tom-f-oconnell/firepick-delta/docs/STL images/3D0015a - EMC02 mounting plate.png

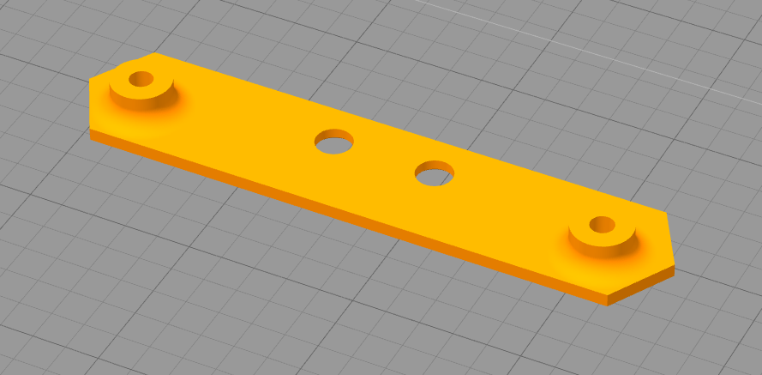
docs/STL images/3D0015a - EMC02 mounting plate.png
