tom-f-oconnell/firepick-delta/docs/STL images/3D0021 - EMC01 Modular tool card-cage.png

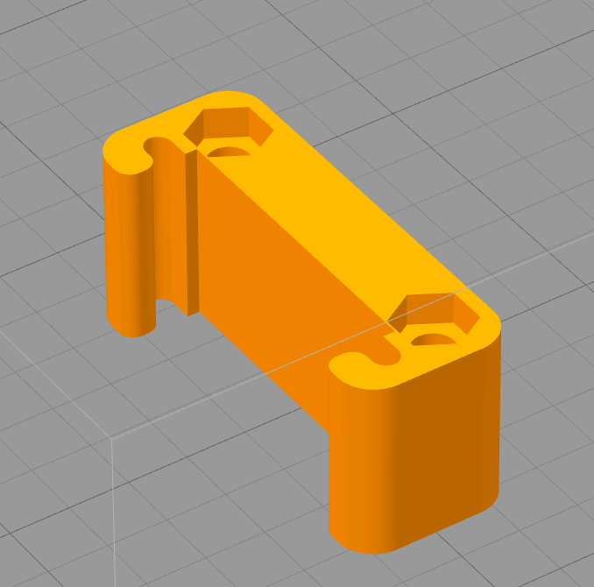
docs/STL images/3D0021 - EMC01 Modular tool card-cage.png
