tom-f-oconnell/firepick-delta/docs/STL images/3D0052a - Heated Bed Bracket.png

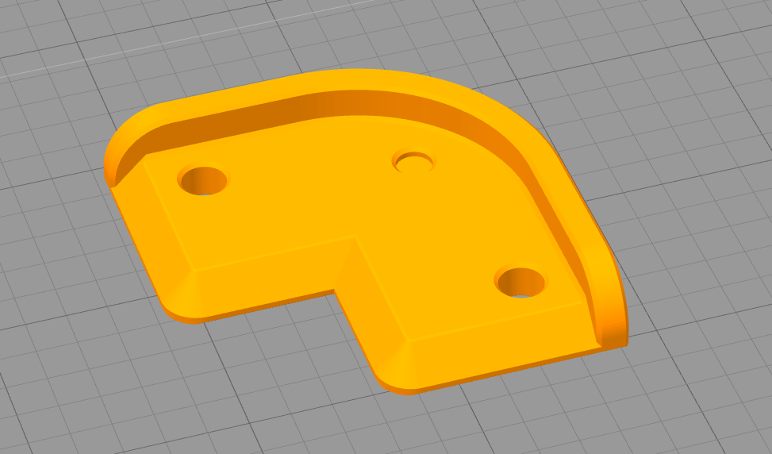
docs/STL images/3D0052a - Heated Bed Bracket.png
