tom-f-oconnell/firepick-delta/docs/STL images/3D0456c Delta stepper mount.png

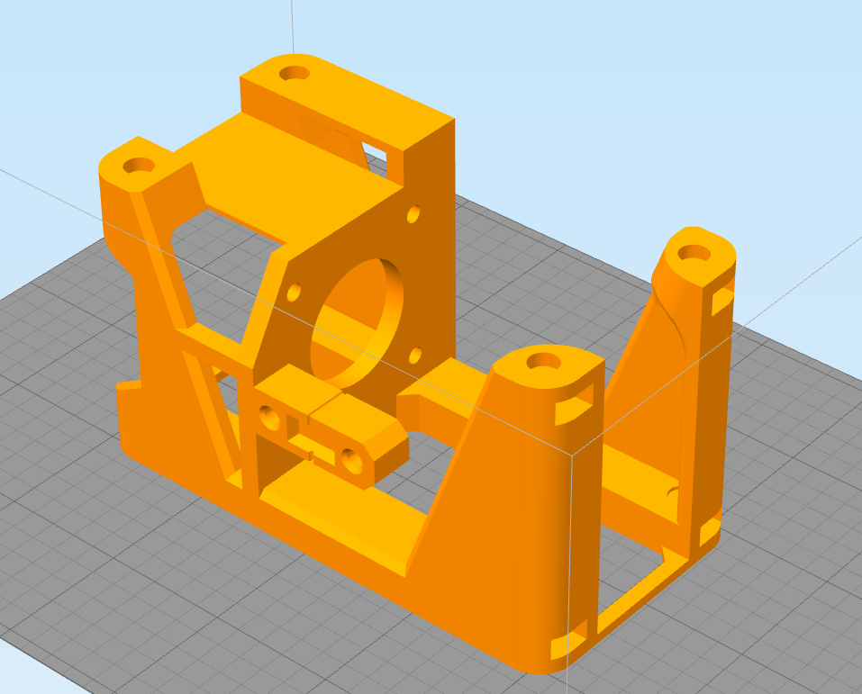
docs/STL images/3D0456c Delta stepper mount.png
