tom-f-oconnell/firepick-delta/docs/STL images/3DAT0001a - Wade extruder body.png

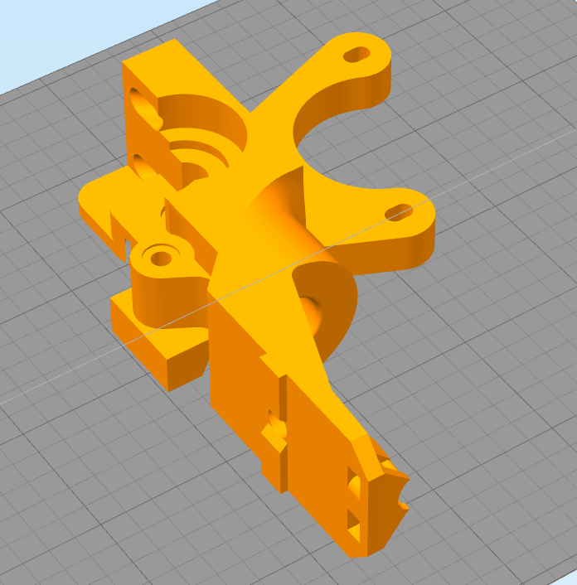
docs/STL images/3DAT0001a - Wade extruder body.png
