tom-f-oconnell/firepick-delta/docs/STL images/3DAT0002 - Wade large gear (herringbone).png

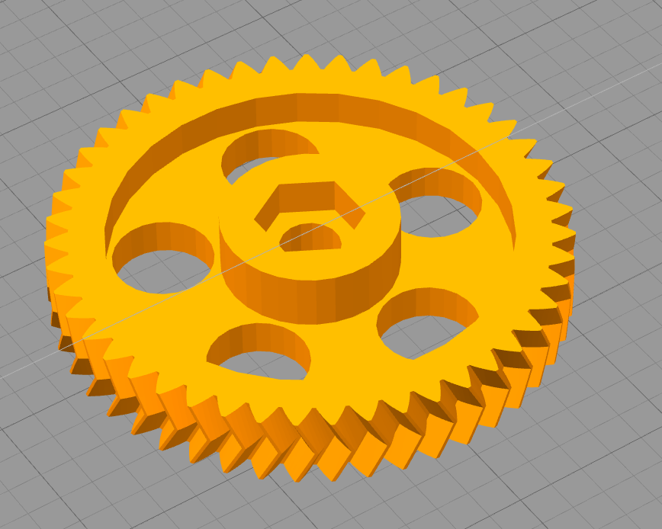
docs/STL images/3DAT0002 - Wade large gear (herringbone).png
