tom-f-oconnell/firepick-delta/docs/STL images/3DAT0003 - Wade small gear (herringbone).png

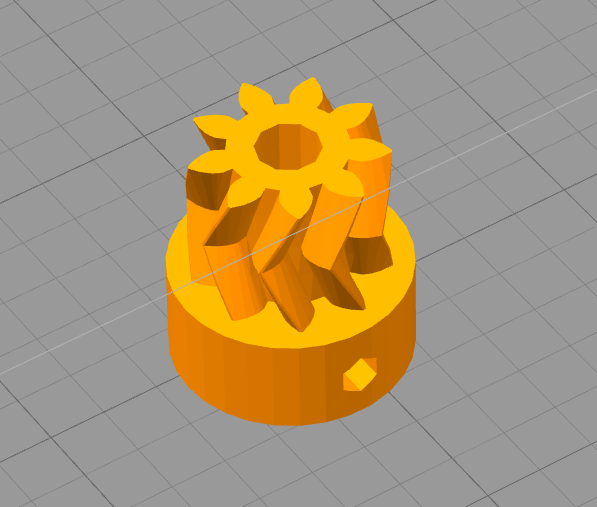
docs/STL images/3DAT0003 - Wade small gear (herringbone).png
