tom-f-oconnell/firepick-delta/docs/STL images/3DAT004 - Guidler.png

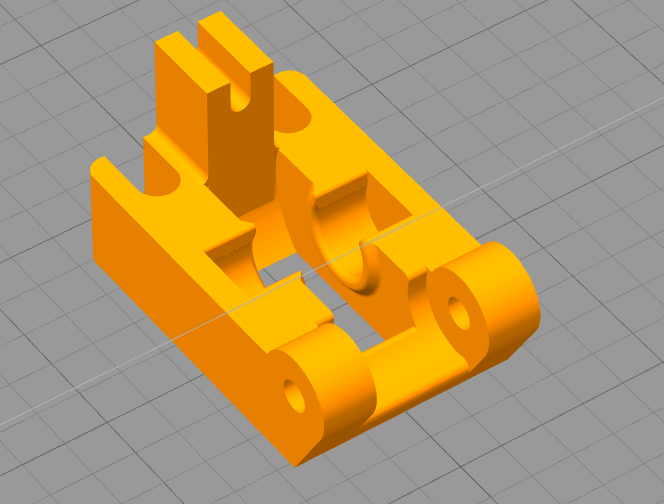
docs/STL images/3DAT004 - Guidler.png
