tom-f-oconnell/firepick-delta/docs/STL images/3DAT0011a - End effector - ATC hub (top).png

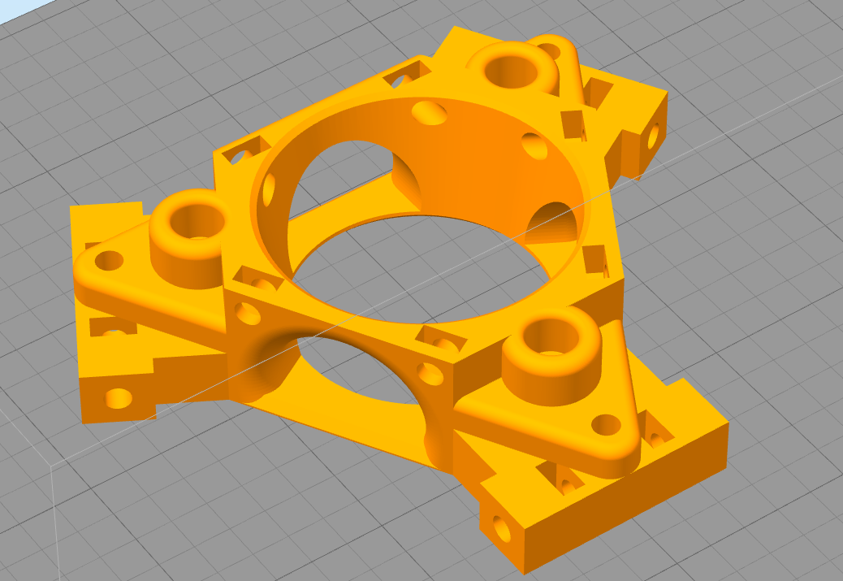
docs/STL images/3DAT0011a - End effector - ATC hub (top).png
