tom-f-oconnell/firepick-delta/docs/STL images/3DAT0015c - Camera-to-end-effector mount - downward endocam.png

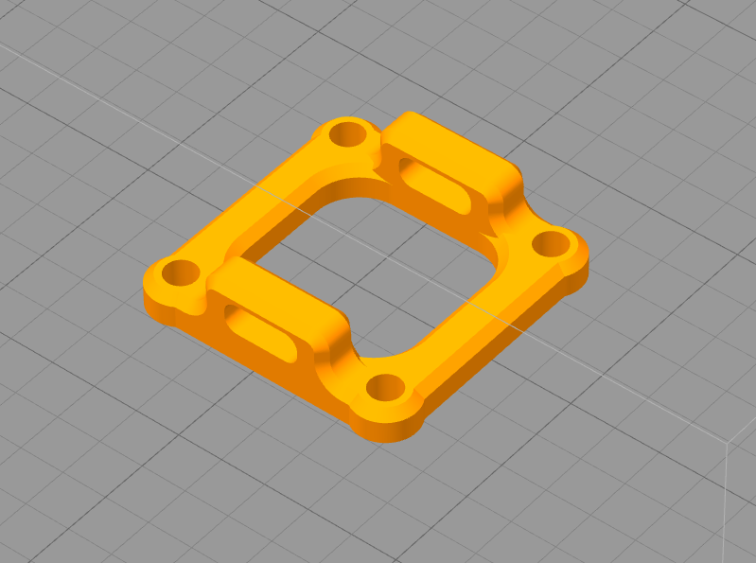
docs/STL images/3DAT0015c - Camera-to-end-effector mount - downward endocam.png
