tom-f-oconnell/firepick-delta/docs/STL images/3DAT0021a - NEMA8 mount.png

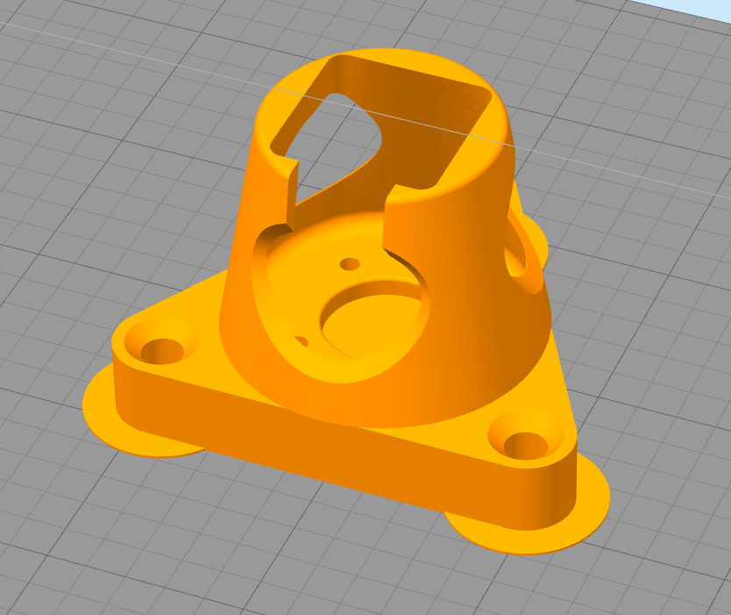
docs/STL images/3DAT0021a - NEMA8 mount.png
