tom-f-oconnell/firepick-delta/docs/STL images/FSTN-M3-14L-UNTHREADED.png

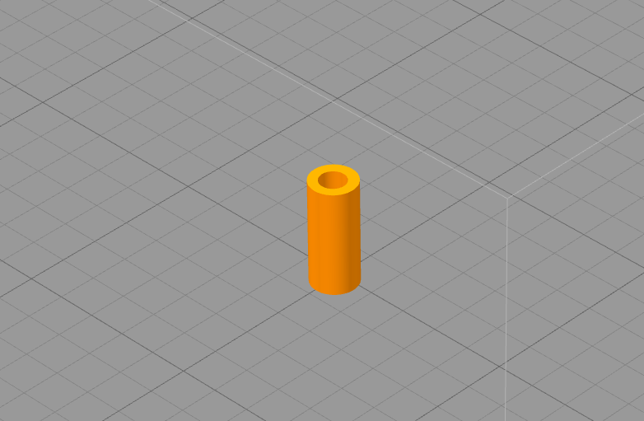
docs/STL images/FSTN-M3-14L-UNTHREADED.png
