tom-f-oconnell/firepick-delta/production/3D printed pieces - STL - Orange/3DAT0015c - Camera-to-end-effector mount - downward endocam.stl

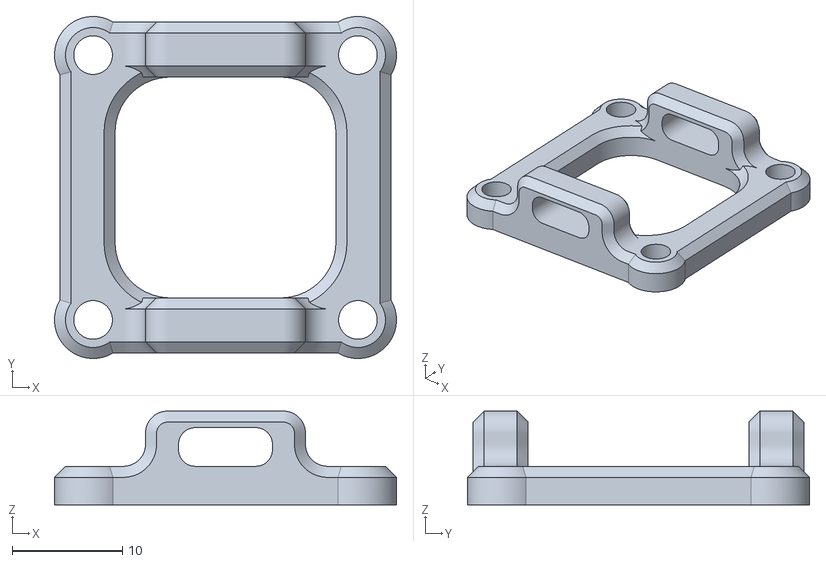
[picture p34: CAD file, 2017-01-31]
production/3D printed pieces - STL - Orange/3DAT0015c - Camera-to-end-effector mount - downward endocam.stl
31.0 x 31.0 x 8.50
