tom-f-oconnell/firepick-delta/production/3D printed pieces - STL - Black/FSTN-M3-16L-UNTHREADED.stl

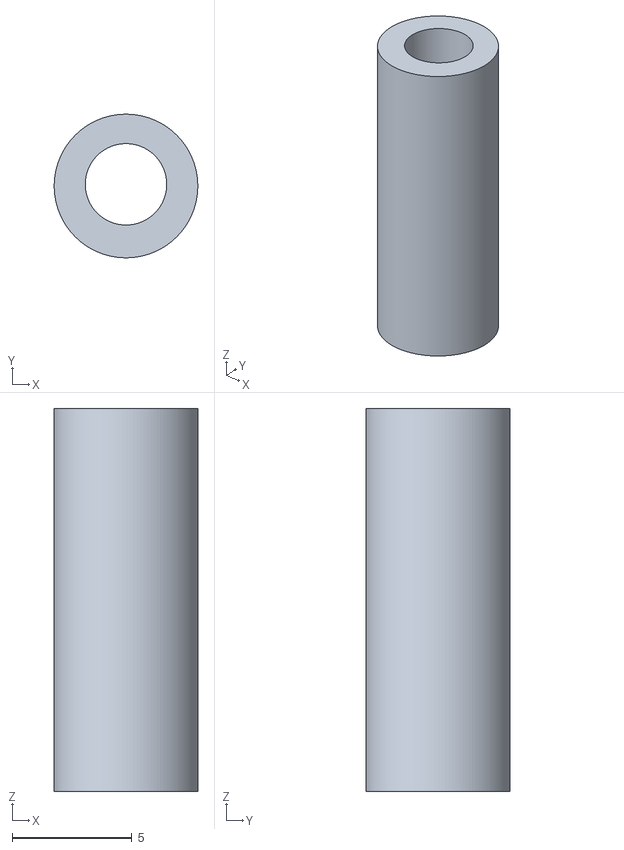
[picture p35: CAD file, 2017-01-31]
production/3D printed pieces - STL - Black/FSTN-M3-16L-UNTHREADED.stl
6.00 x 6.00 x 16.0
