tom-f-oconnell/firepick-delta/production/3D printed pieces - STL - Orange/3DAT0017 - 3D printer mount - J-Head (top).stl

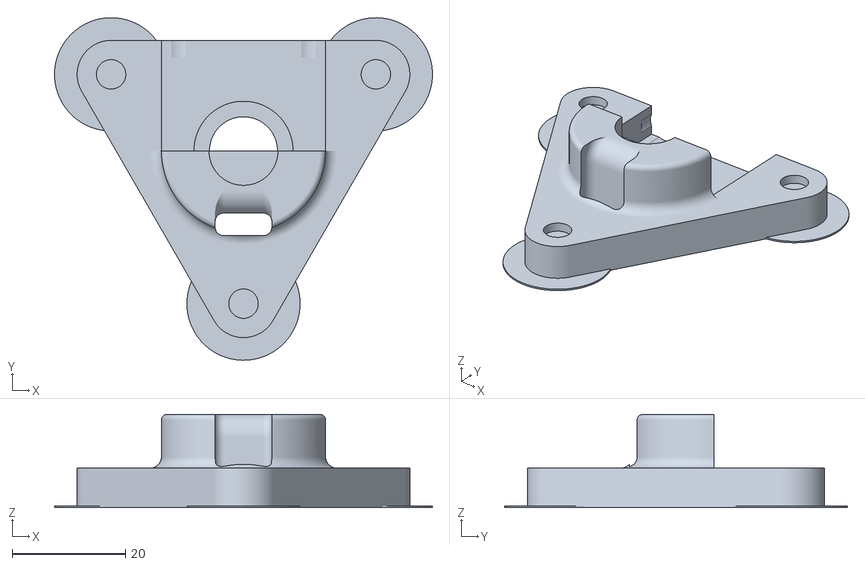
[picture p36: CAD file, 2017-01-31]
production/3D printed pieces - STL - Orange/3DAT0017 - 3D printer mount - J-Head (top).stl
66.8 x 60.5 x 16.5
