tom-f-oconnell/firepick-delta/production/3D printed pieces - STL - Black/vial_funnel.stl

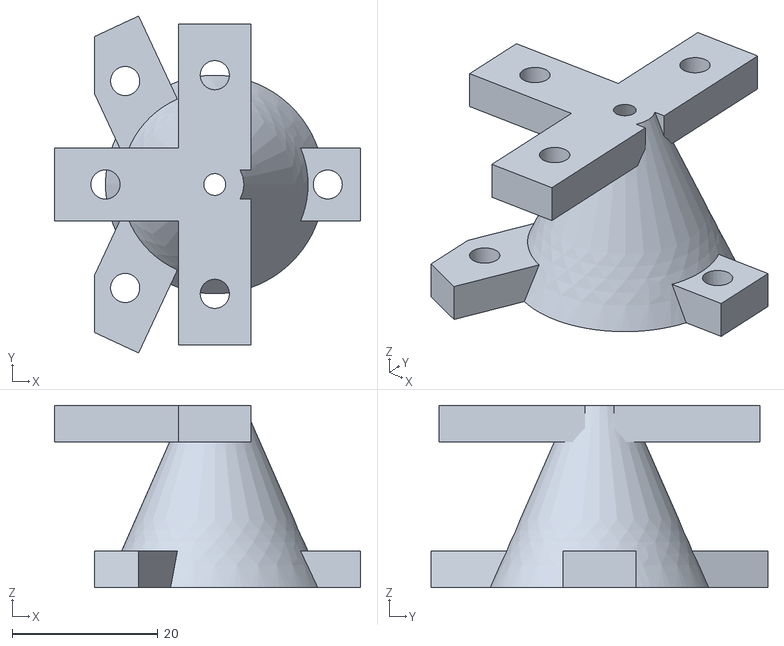
[picture p37: CAD file, 2017-01-31]
production/3D printed pieces - STL - Black/vial_funnel.stl
42.0 x 46.3 x 25.0
