tom-f-oconnell/firepick-delta/production/3D printed pieces - STL - Orange/3DAT0021a - NEMA8 mount.stl

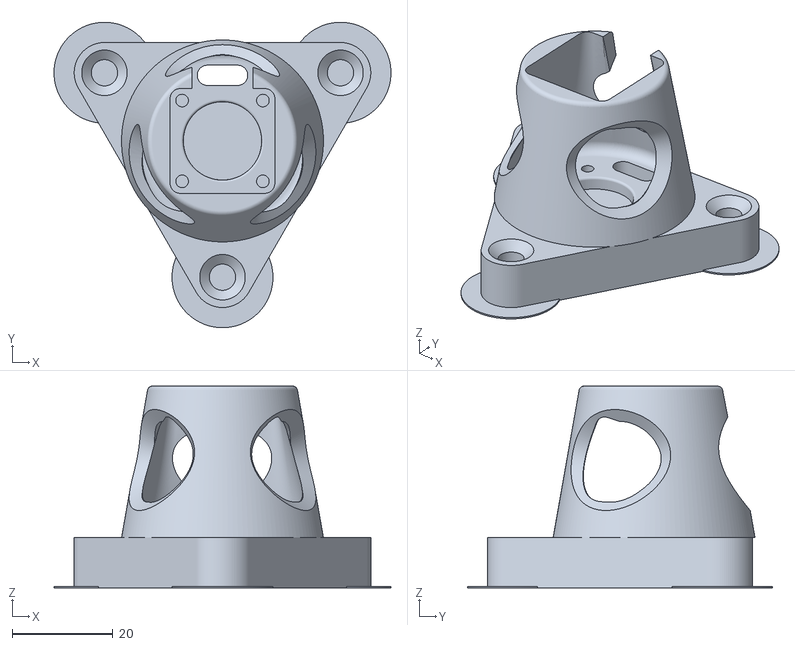
[picture p38: CAD file, 2017-01-31]
production/3D printed pieces - STL - Orange/3DAT0021a - NEMA8 mount.stl
66.8 x 60.5 x 40.0
