tom-f-oconnell/firepick-delta/production/3D printed pieces - STL - Black/FSTN-M3-14L-UNTHREADED.stl

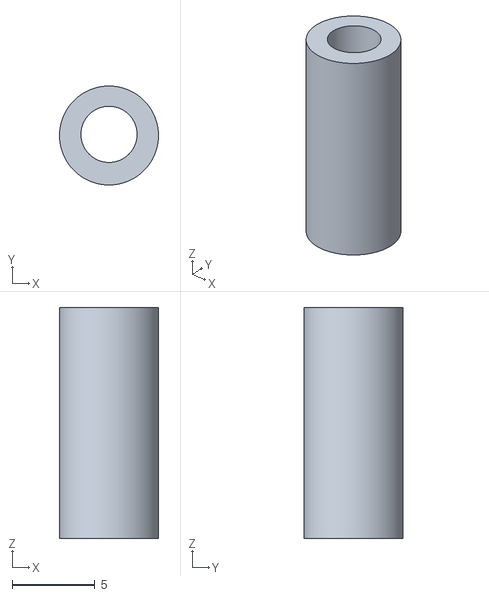
[picture p39: CAD file, 2017-01-31]
production/3D printed pieces - STL - Black/FSTN-M3-14L-UNTHREADED.stl
6.00 x 6.00 x 14.0
