tom-f-oconnell/firepick-delta/production/3D printed pieces - STL - Orange/3D0053 - External ATX supply coverplate.stl

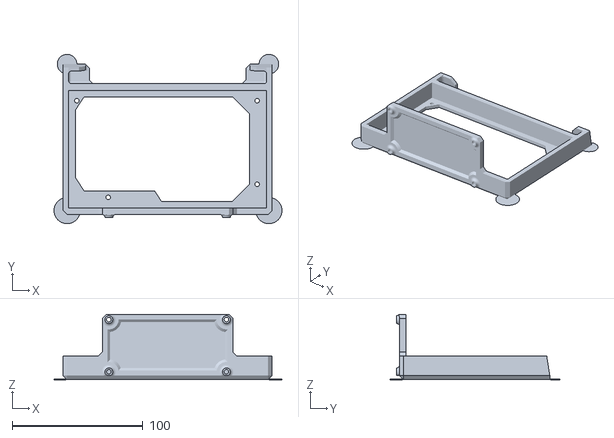
[picture p40: CAD file, 2017-01-31]
production/3D printed pieces - STL - Orange/3D0053 - External ATX supply coverplate.stl
174.5 x 129.6 x 50.0
