tom-f-oconnell/firepick-delta/production/3D printed pieces - STL - Orange/3D0024 - Delta rods - Upper spring-socket holder.stl

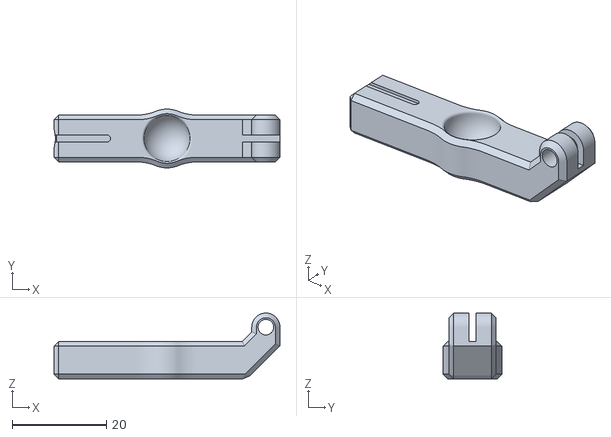
[picture p41: CAD file, 2017-01-31]
production/3D printed pieces - STL - Orange/3D0024 - Delta rods - Upper spring-socket holder.stl
48.0 x 12.5 x 14.0
