tom-f-oconnell/firepick-delta/production/3D printed pieces - STL - Black/3DAT0003 - Wade small gear (herringbone).stl

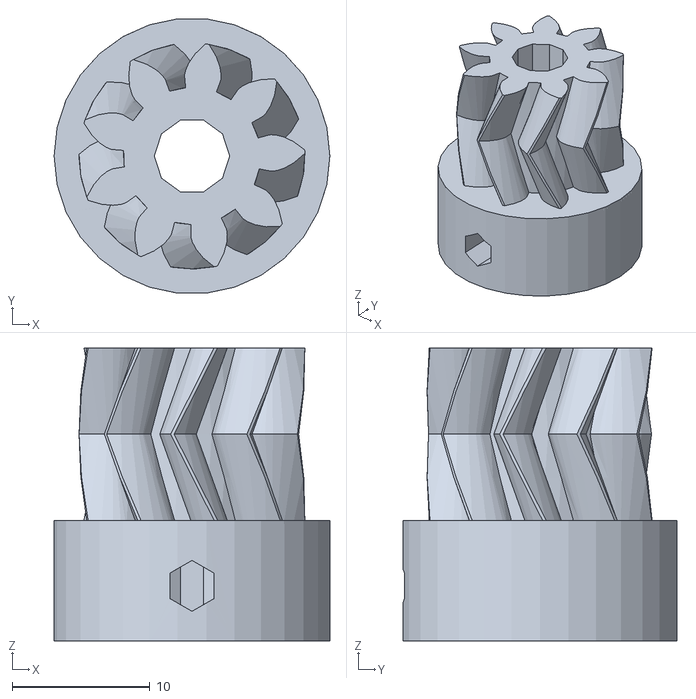
[picture p42: CAD file, 2017-01-31]
production/3D printed pieces - STL - Black/3DAT0003 - Wade small gear (herringbone).stl
20.0 x 19.9 x 21.2
