tom-f-oconnell/firepick-delta/production/3D printed pieces - STL - Black/3DAT0012a - 3D printer mount.stl

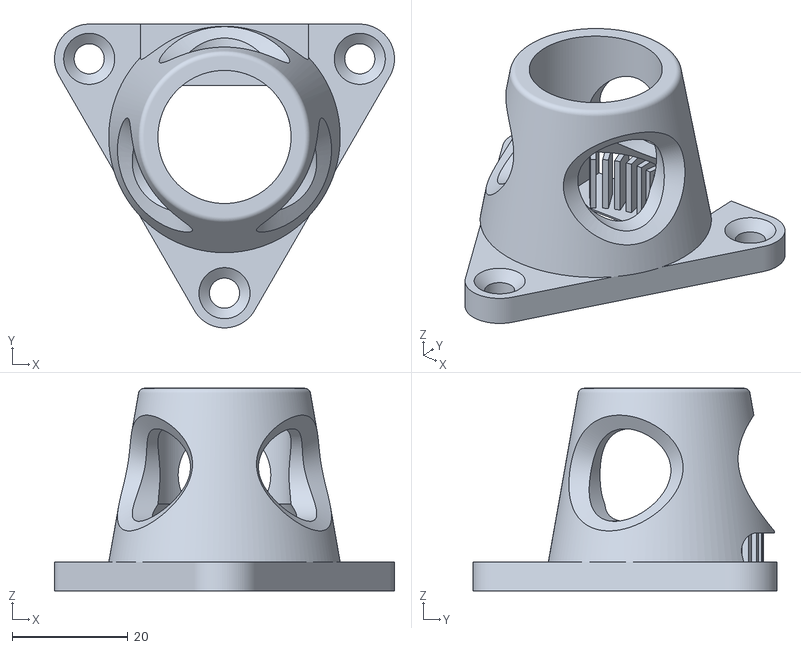
[picture p43: CAD file, 2017-01-31]
production/3D printed pieces - STL - Black/3DAT0012a - 3D printer mount.stl
58.8 x 52.5 x 35.0
