tom-f-oconnell/firepick-delta/production/3D printed pieces - STL - Black/3DAT0005 - Vacuum pump mount.stl

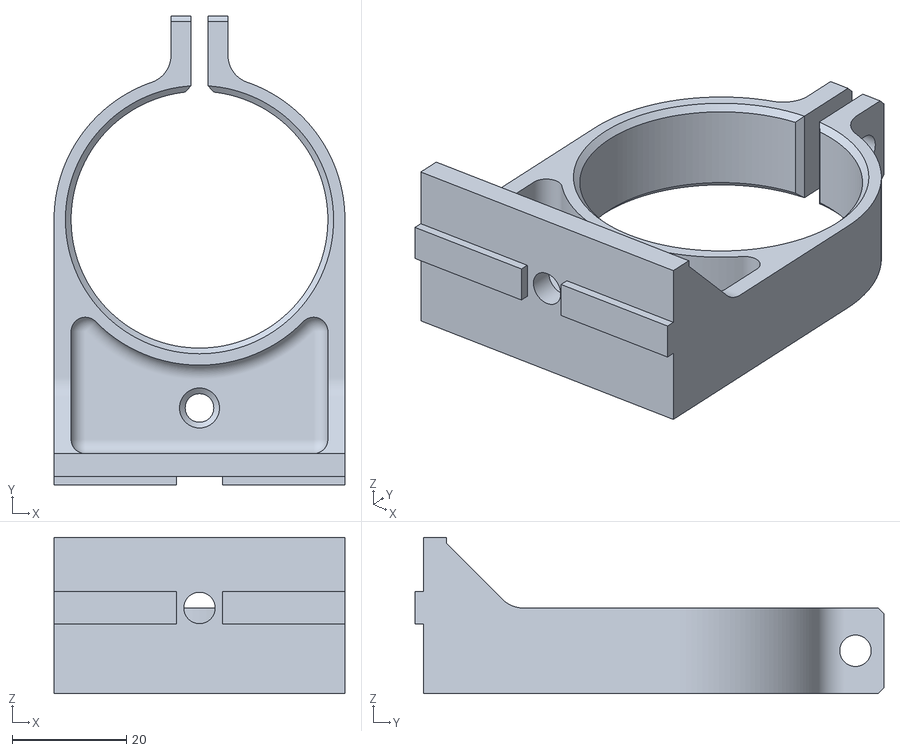
[picture p44: CAD file, 2017-01-31]
production/3D printed pieces - STL - Black/3DAT0005 - Vacuum pump mount.stl
51.0 x 82.2 x 27.4
