tom-f-oconnell/firepick-delta/production/3D printed pieces - STL - Black/3DAC0009 - Feeder - Bed mount manual (8mm).stl

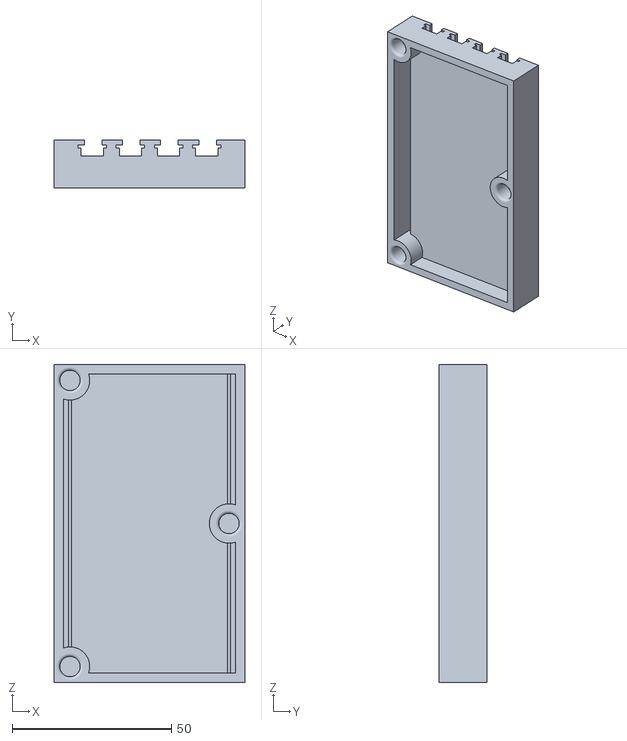
[picture p45: CAD file, 2017-01-31]
production/3D printed pieces - STL - Black/3DAC0009 - Feeder - Bed mount manual (8mm).stl
60.0 x 15.0 x 100.0
