tom-f-oconnell/firepick-delta/production/3D printed pieces - STL - Black/3D0456 Delta stepper mount (unibody).stl

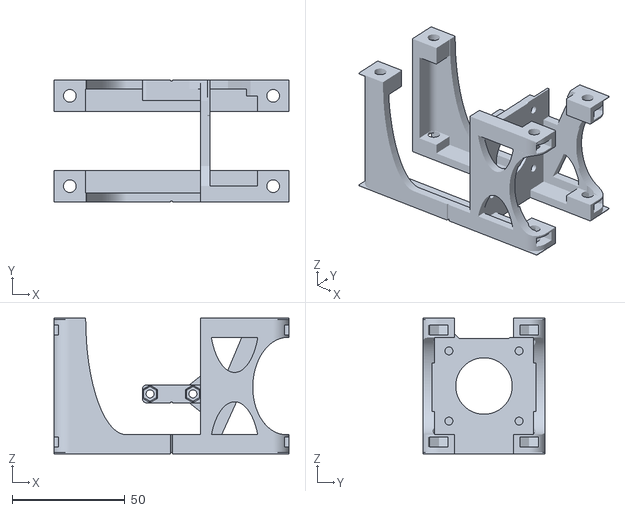
[picture p46: CAD file, 2017-01-31]
production/3D printed pieces - STL - Black/3D0456 Delta stepper mount (unibody).stl
104.0 x 54.1 x 60.0
