tom-f-oconnell/firepick-delta/production/3D printed pieces - STL - Black/3DAT0027 - Extruder latch.stl

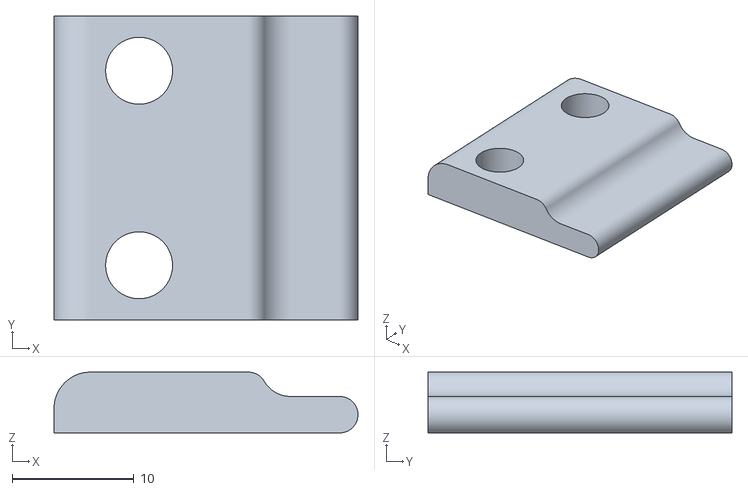
[picture p47: CAD file, 2017-01-31]
production/3D printed pieces - STL - Black/3DAT0027 - Extruder latch.stl
25.0 x 25.0 x 5.00
