tom-f-oconnell/firepick-delta/production/3D printed pieces - STL - Black/3D0456b Delta stepper mount.stl

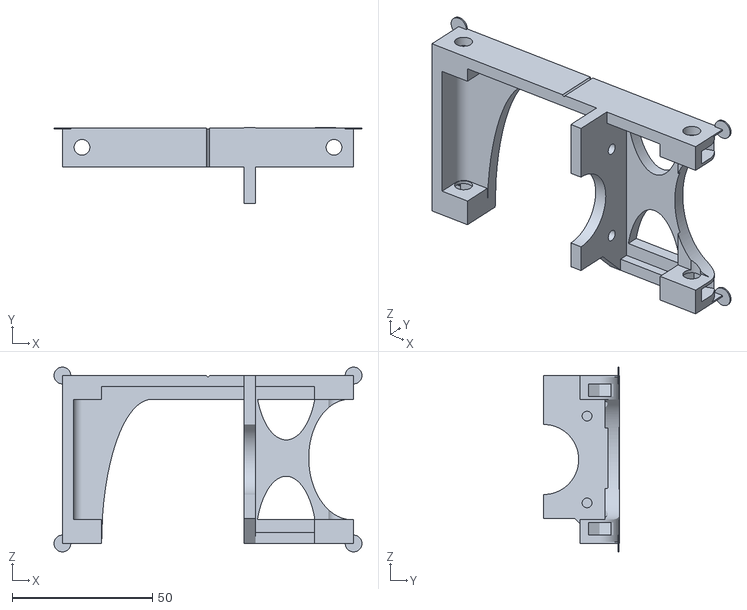
[picture p48: CAD file, 2017-01-31]
production/3D printed pieces - STL - Black/3D0456b Delta stepper mount.stl
110.0 x 27.0 x 66.0
