tom-f-oconnell/firepick-delta/production/3D printed pieces - STL - Black/3DAT004 - Guidler.stl

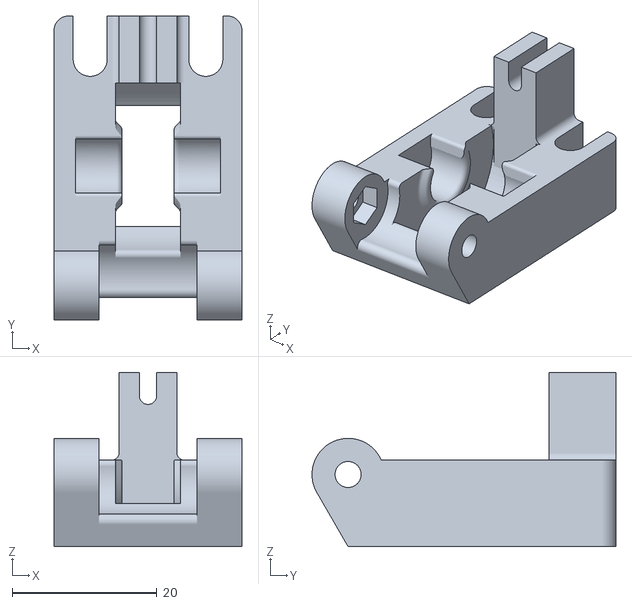
[picture p49: CAD file, 2017-01-31]
production/3D printed pieces - STL - Black/3DAT004 - Guidler.stl
26.0 x 42.1 x 24.1
