tom-f-oconnell/firepick-delta/production/3D printed pieces - STL - Black/3D0456c Delta stepper mount.stl

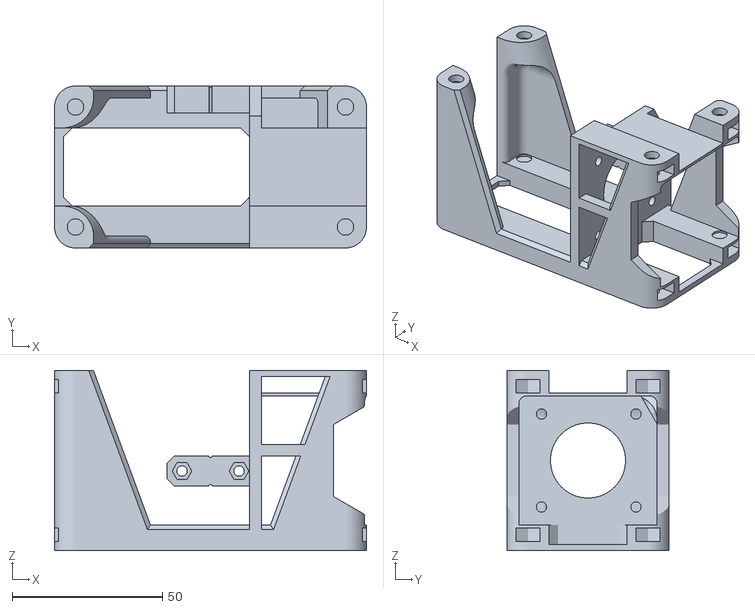
[picture p50: CAD file, 2017-01-31]
production/3D printed pieces - STL - Black/3D0456c Delta stepper mount.stl
104.0 x 54.0 x 60.0
