tom-f-oconnell/firepick-delta/production/3D printed pieces - STL - Black/vial_susan_pulley.stl

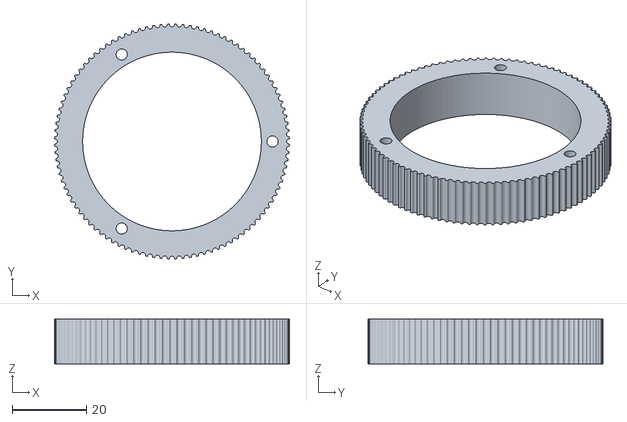
[picture p51: CAD file, 2017-01-31]
production/3D printed pieces - STL - Black/vial_susan_pulley.stl
63.1 x 63.1 x 12.0
