tom-f-oconnell/firepick-delta/production/3D printed pieces - STL - Black/arm_bracket_lower_5mm_diam_ball.stl

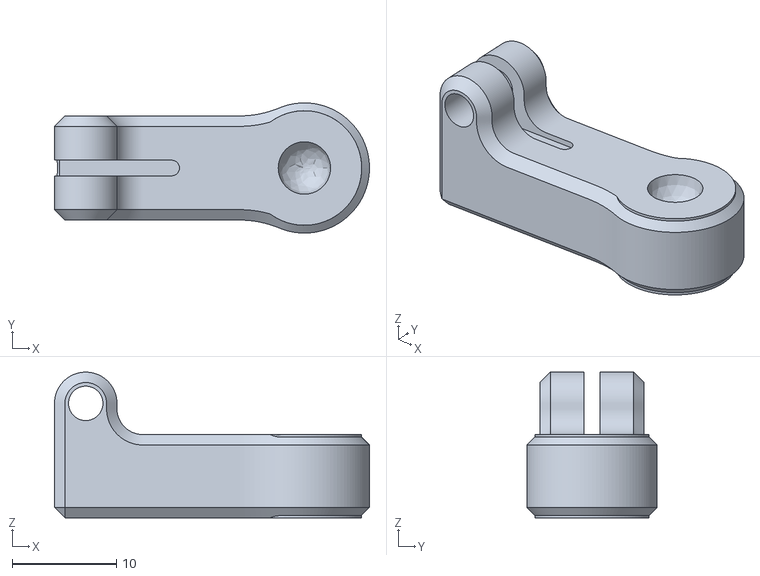
[picture p52: CAD file, 2017-01-31]
production/3D printed pieces - STL - Black/arm_bracket_lower_5mm_diam_ball.stl
30.2 x 12.5 x 14.0
