tom-f-oconnell/firepick-delta/production/3D printed pieces - STL - Black/3D0021 - EMC01 Modular tool card-cage.stl

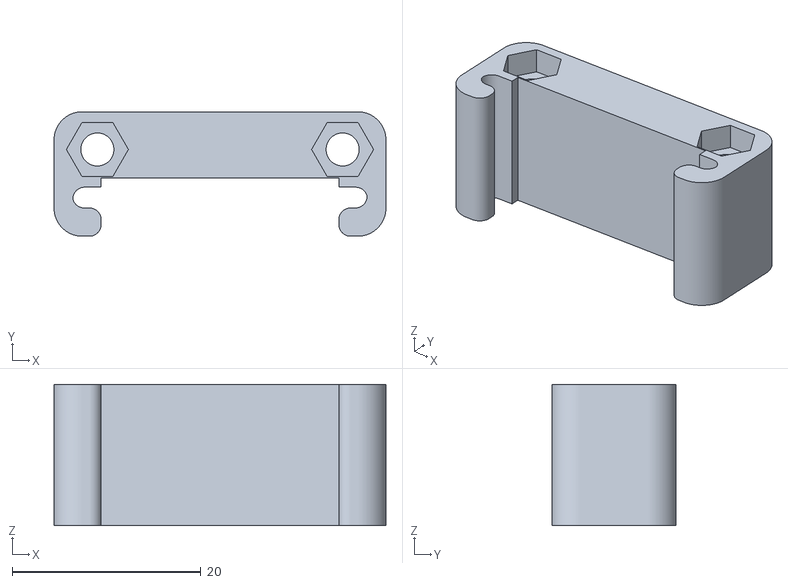
[picture p53: CAD file, 2017-01-31]
production/3D printed pieces - STL - Black/3D0021 - EMC01 Modular tool card-cage.stl
35.2 x 13.2 x 15.0
