tom-f-oconnell/firepick-delta/production/3D printed pieces - STL - Black/nidec_22h_bracket.stl

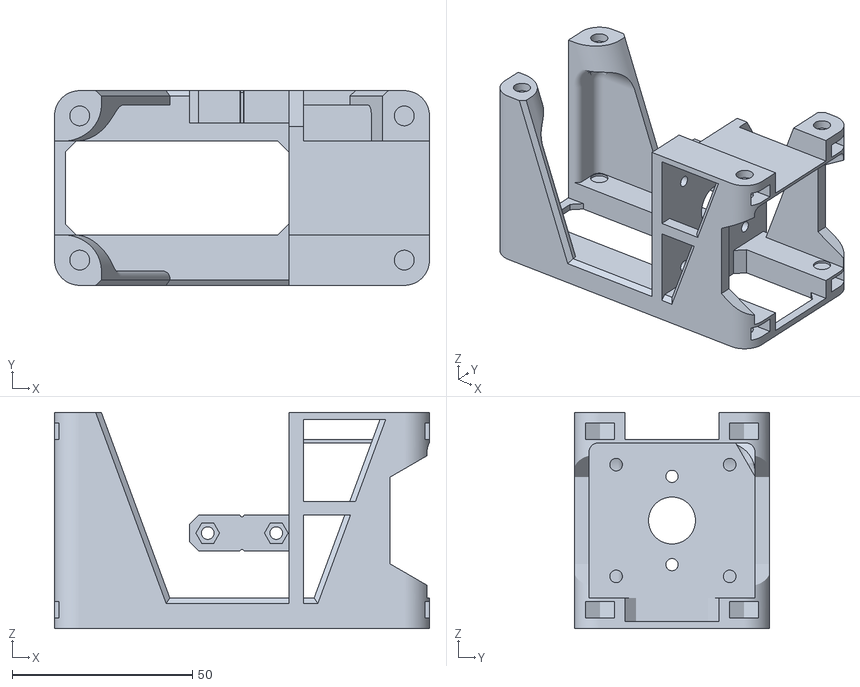
[picture p54: CAD file, 2017-01-31]
production/3D printed pieces - STL - Black/nidec_22h_bracket.stl
104.0 x 54.0 x 60.0
