tom-f-oconnell/firepick-delta/production/3D printed pieces - STL - Black/3DAT0001a - Wade extruder body.stl

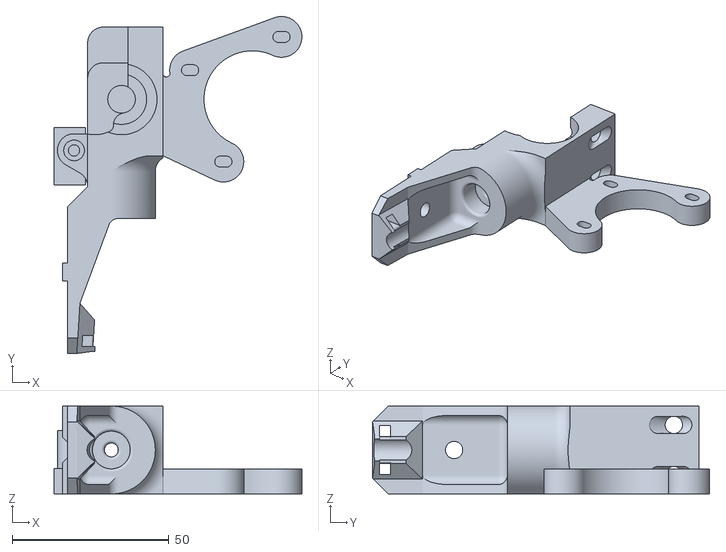
[picture p55: CAD file, 2017-01-31]
production/3D printed pieces - STL - Black/3DAT0001a - Wade extruder body.stl
79.0 x 107.4 x 28.0
