tom-f-oconnell/firepick-delta/production/3D printed pieces - STL - Black/3D0028 - PCB magnet holder.stl

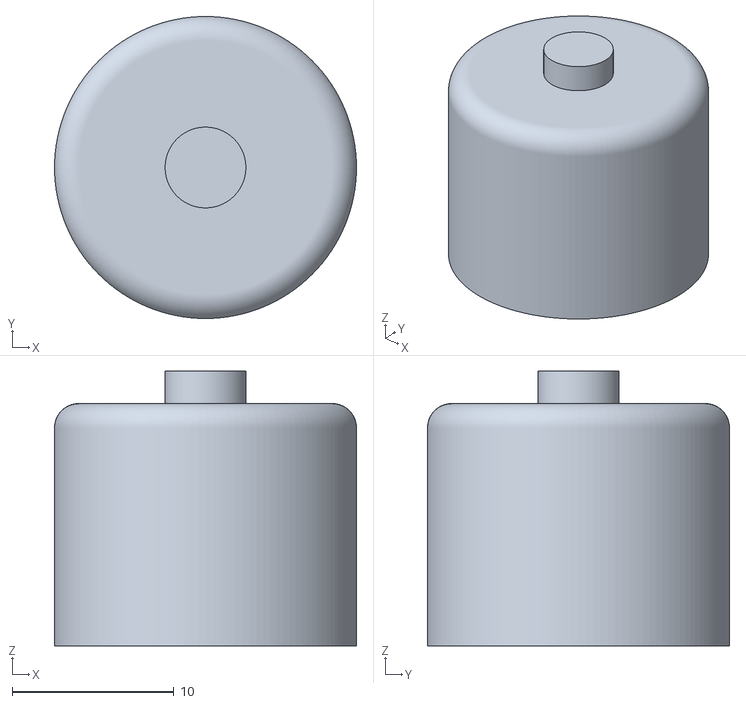
[picture p56: CAD file, 2017-01-31]
production/3D printed pieces - STL - Black/3D0028 - PCB magnet holder.stl
18.7 x 18.7 x 17.0
