tom-f-oconnell/firepick-delta/production/3D printed pieces - STL - Black/arm_bracket_upper_5mm_diam_ball.stl

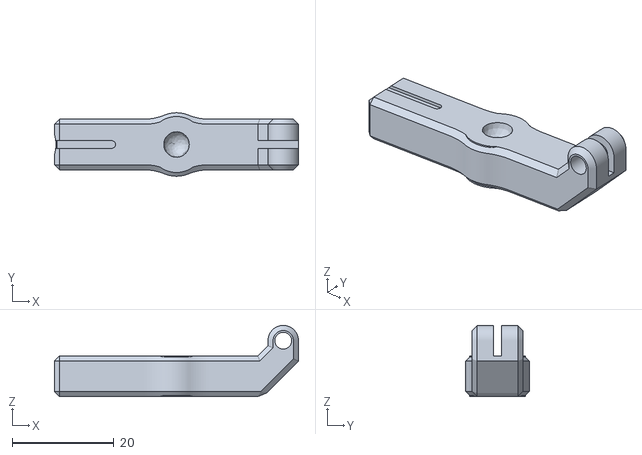
[picture p57: CAD file, 2017-01-31]
production/3D printed pieces - STL - Black/arm_bracket_upper_5mm_diam_ball.stl
48.0 x 12.5 x 14.0
