tom-f-oconnell/firepick-delta/production/3D printed pieces - STL - Black/3D0026b - Up-looking camera housing base - ELP-USB100W03M.stl

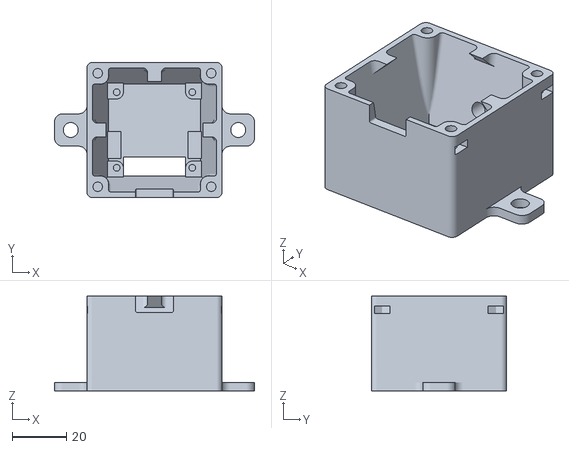
[picture p58: CAD file, 2017-01-31]
production/3D printed pieces - STL - Black/3D0026b - Up-looking camera housing base - ELP-USB100W03M.stl
74.0 x 50.0 x 35.0
