tom-f-oconnell/firepick-delta/production/3D printed pieces - STL - Black/Tool Holder.stl

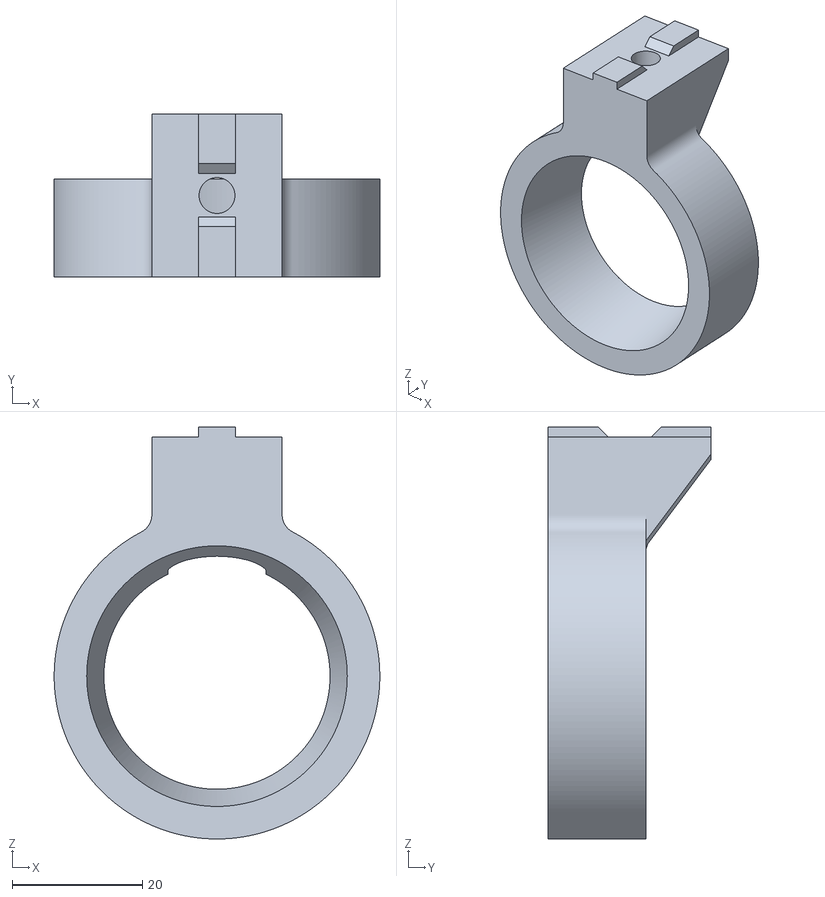
[picture p59: CAD file, 2017-01-31]
production/3D printed pieces - STL - Black/Tool Holder.stl
50.0 x 25.0 x 63.2
