tom-f-oconnell/firepick-delta/production/3D printed pieces - STL - Black/vial_susan_servo_pulley.stl

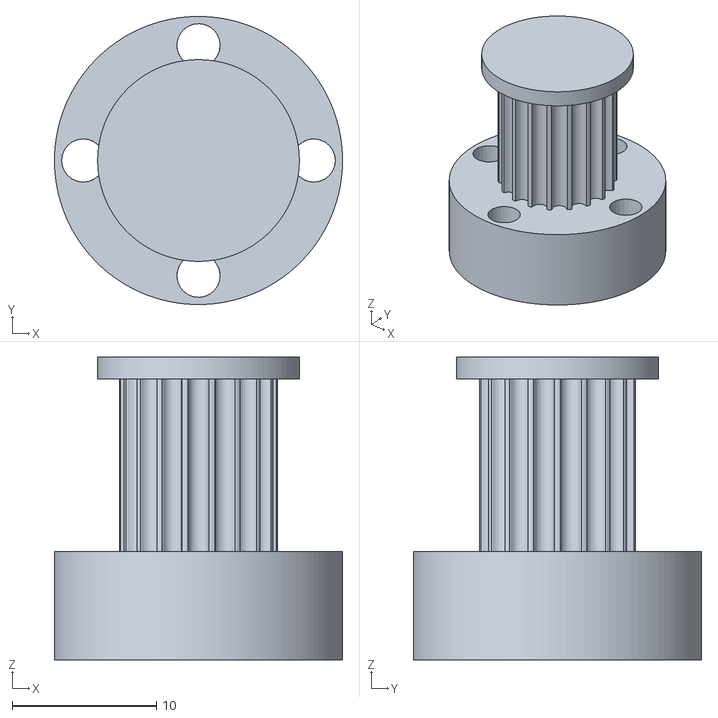
[picture p61: CAD file, 2017-01-31]
production/3D printed pieces - STL - Black/vial_susan_servo_pulley.stl
20.0 x 20.0 x 21.0
