tom-f-oconnell/firepick-delta/production/3D printed pieces - STL - Black/3D0456ab Delta stepper mount.stl

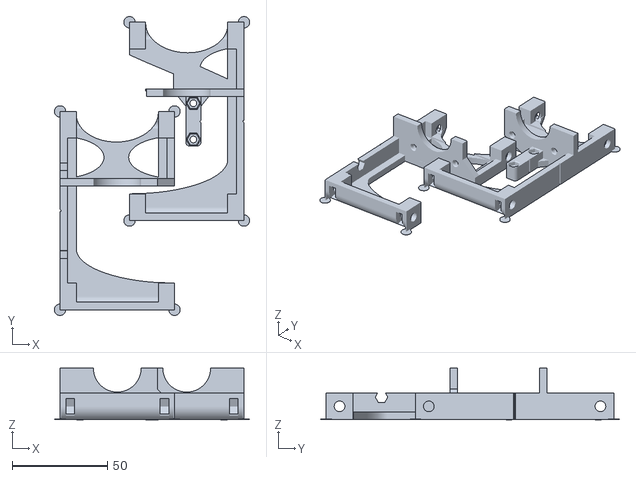
[picture p62: CAD file, 2017-01-31]
production/3D printed pieces - STL - Black/3D0456ab Delta stepper mount.stl
102.4 x 156.8 x 27.0
