tom-f-oconnell/firepick-delta/docs/STL images/3D0001a - Delta motor Assembly - 608 bearing block.png

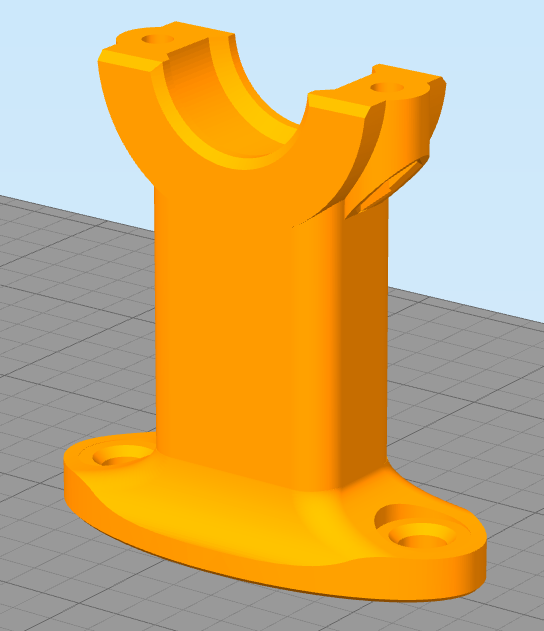
docs/STL images/3D0001a - Delta motor Assembly - 608 bearing block.png
