tom-f-oconnell/firepick-delta/docs/STL images/3D0003a - Delta motor assembly - Delta arm 90mm.png

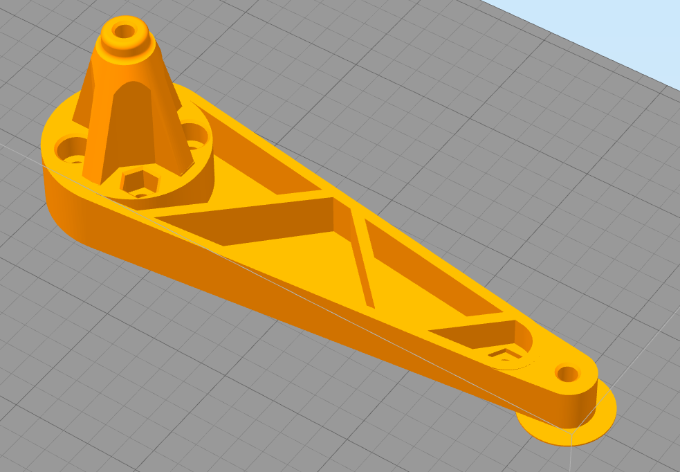
docs/STL images/3D0003a - Delta motor assembly - Delta arm 90mm.png
