tom-f-oconnell/firepick-delta/docs/STL images/3D0003b - Delta motor assembly - Delta arm 90mm nut.png

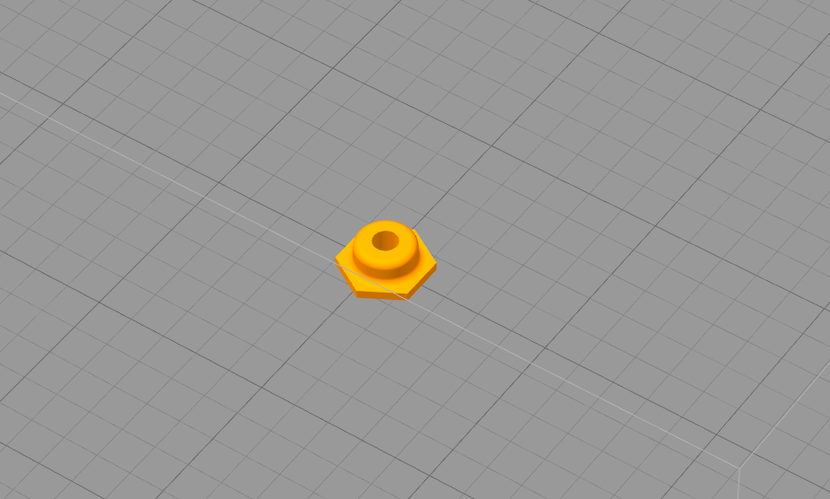
docs/STL images/3D0003b - Delta motor assembly - Delta arm 90mm nut.png
