tom-f-oconnell/firepick-delta/docs/STL images/3D0004 - Delta motor Assembly - 608 bearing block caps.png

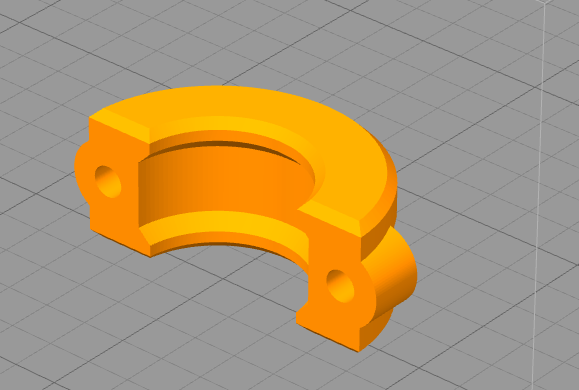
docs/STL images/3D0004 - Delta motor Assembly - 608 bearing block caps.png
