tom-f-oconnell/firepick-delta/docs/STL images/3D0007 - Delta motor assembly - Limit switch interruptor.png

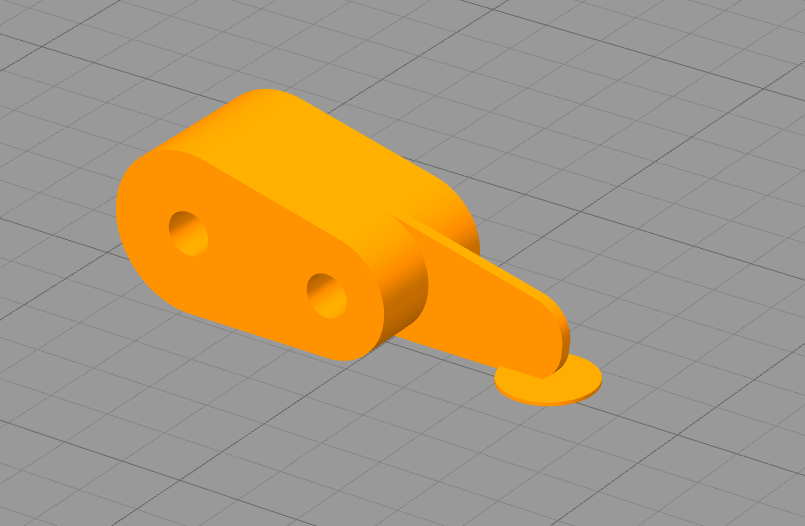
docs/STL images/3D0007 - Delta motor assembly - Limit switch interruptor.png
