tom-f-oconnell/firepick-delta/docs/STL images/3DAT0012a - 3D printer mount.png

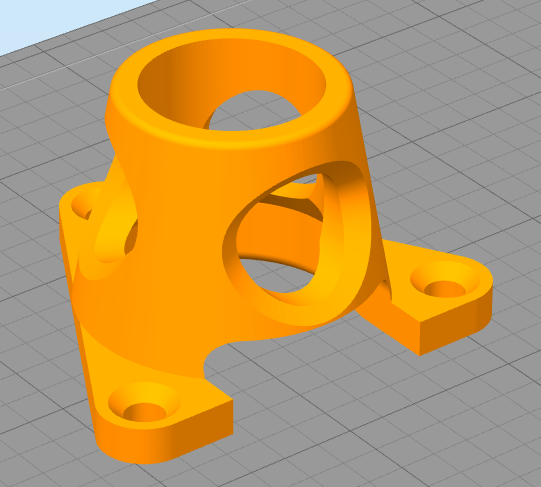
docs/STL images/3DAT0012a - 3D printer mount.png
