tom-f-oconnell/firepick-delta/docs/STL images/3DAT0017 - 3D printer mount - J-Head (top).png

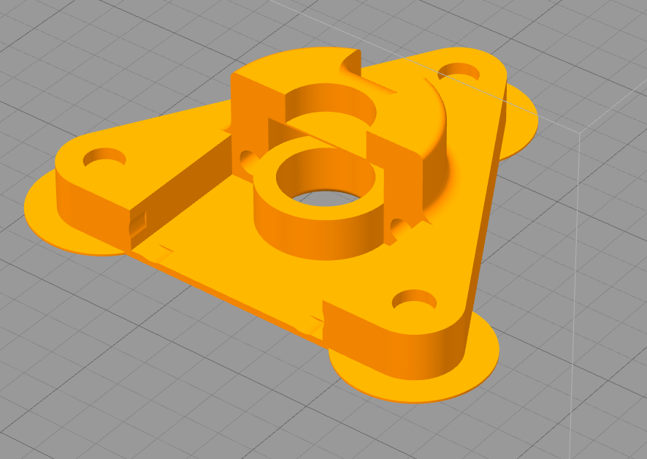
docs/STL images/3DAT0017 - 3D printer mount - J-Head (top).png
