tom-f-oconnell/firepick-delta/docs/STL images/3DAT0018a - 3D printer mount - J-Head (clamp).png

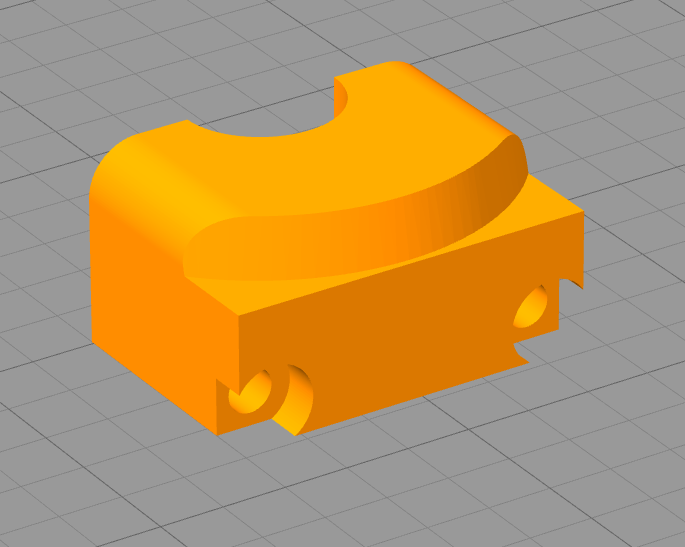
docs/STL images/3DAT0018a - 3D printer mount - J-Head (clamp).png
